ShrinathN/ThermalSampler/sims/current_sim.asc

C2: cap; 220µ
I1: load2; PWL file=radio_energy_profile.pwl
I2: load2; 5µ
R1: res; 3k
V1: voltage; 3
Named nets: 0, VRAIL
.tran 10
Assume a CR2032 cell
Limits max discharge 
current to 3mA
To simulated 5uA
MCU sleep current
Actual real world recording
of radio current consumption
